weerachai8266/CWT-Thread-Verification/IMG/ESP32-Enable-Pin.png

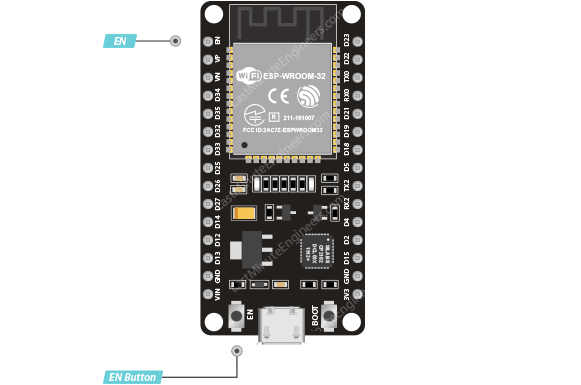
IMG/ESP32-Enable-Pin.png
