weerachai8266/CWT-Thread-Verification/IMG/ESP32-RTC-GPIO-Pins.png

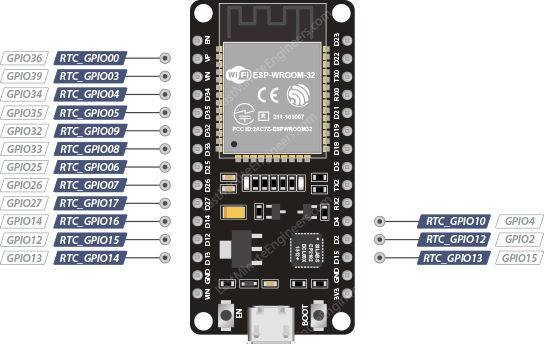
IMG/ESP32-RTC-GPIO-Pins.png
