weerachai8266/CWT-Thread-Verification/IMG/ESP32-Strapping-Pins.png

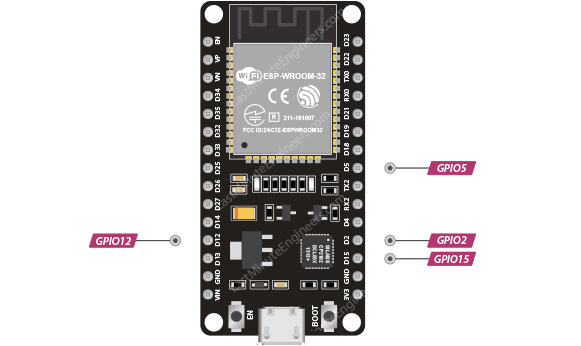
IMG/ESP32-Strapping-Pins.png
