weerachai8266/CWT-Thread-Verification/docs/User Manual for Barcode Scanner/GM802 Series Barcode reader module User Manual-V1.2.1/GM802 Reference Circuit Diagram.pdf

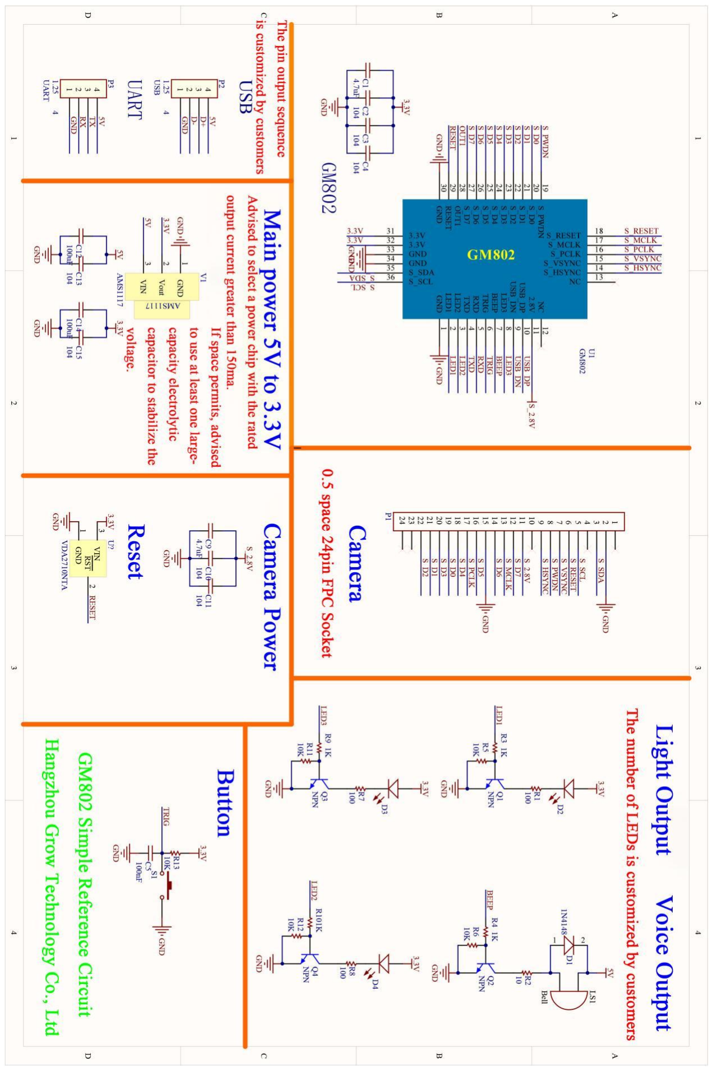
[picture p8: figure]
